Cuprum77/PD2Breadboard/Software/include/bg.h

/* GIMP RGB C-Source image dump (bg.c) */

static const unsigned char background_image[] =
  "\343\030\343\030\343\030\343\030\343\030\343\030\343\030\343\030\343\030\343\030\343"
  "\030\343\030\343\030\343\030\343\030\343\030\343\030\343\030\343\030\343\030\343\030"
  "\343\030\343\030\343\030\343\030\343\030\343\030\343\030\343\030\343\030\343\030\343"
  "\030\343\030\343\030\343\030\343\030\343\030\343\030\343\030\343\030\343\030\343\030"
  "\343\030\343\030\343\030\343\030\343\030\343\030\343\030\343\030\343\030\343\030\343"
  "\030\343\030\343\030\343\030\343\030\343\030\343\030\343\030\343\030\343\030\343\030"
  "\343\030\343\030\343\030\343\030\343\030\343\030\343\030\343\030\343\030\343\030\343"
  "\030\343\030\343\030\343\030\343\030\343\030\343\030\343\030\343\030\343\030\343\030"
  "\343\030\343\030\343\030\343\030\343\030\343\030\343\030\343\030\343\030\343\030\343"
  "\030\343\030\343\030\343\030\343\030\343\030\343\030\343\030\343\030\343\030\343\030"
  "\343\030\343\030\343\030\343\030\343\030\343\030\343\030\343\030\343\030\343\030\343"
  "\030\343\030\343\030\343\030\343\030\343\030\343\030\343\030\343\030\343\030\343\030"
  "\343\030\343\030\343\030\343\030\343\030\343\030\343\030\343\030\343\030\343\030\343"
  "\030\343\030\343\030\343\030\343\030\343\030\343\030\343\030\343\030\343\030\343\030"
  "\343\030\343\030\343\030\343\030\343\030\343\030\343\030\343\030\343\030\343\030\343"
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
  "\377\377\377\377\377\377\377\377\272\326\343\030\343\030\343\030\343\030\343"
  "\030\343\030\343\030\343\030\343\030\343\030\343\030\343\030\343\030\343\030\343\030"
  "\343\030\343\030\343\030\343\030\343\030\343\030\343\030\343\030\343\030\343\030\343"
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
