Cuprum77/PD2Breadboard/Software/include/test.h

#pragma once
const size_t test_size = 37514;
const unsigned char test[] = {
0x00, 0x00, 0x92, 0x86, 0x01, 0x8c, 0x00, 0x80, 0x80, 0x00, 0x01, 0x02, 0x7e, 0x84, 0x00, 0x9e, 0x00, 0x80, 0x80, 0x00, 0x01, 0x13, 0x75, 0x8f, 0x00, 0x01, 0x33, 0x75, 0x89, 0x00, 0x01, 0x20, 0x76, 0x8b, 0x00, 0x9d, 0x00, 0x80, 0x80, 0x00, 0x01, 0x09, 0x7a, 0x8a, 0x00, 0x01, 0x7b, 0x7b, 0x85, 0x00, 0x01, 0xac, 0x7b, 0x85, 0x00, 0x01, 0x15, 0x73, 0x8d, 0x00, 0x05, 0x00, 0x80, 0x80, 0x00, 0x01, 0x07, 0x7b, 0x8c, 0x00, 0x96, 0x00, 0x80, 0x80, 0x00, 0x01, 0x0e, 0x77, 0x8c, 0x00, 0x01, 0x89, 0x7c, 0x87, 0x00, 0x01, 0xff, 0x80, 0x7f, 0x00, 0x01, 0x5d, 0x79, 0x89, 0x00, 0x01, 0x0b, 0x79, 0x8e, 0x00, 0x04, 0x00, 0x80, 0x80, 0x00, 0x01, 0x1b, 0x75, 0x89, 0x00, 0x01, 0x18, 0x76, 0x8b, 0x00, 0x95, 0x00, 0x80, 0x80, 0x00, 0x01, 0x0e, 0x77, 0x8c, 0x00, 0x01, 0xac, 0x7b, 0x85, 0x00, 0x01, 0xf8, 0x7e, 0x84, 0x00, 0x01, 0xda, 0x7c, 0x82, 0x00, 0x01, 0x15, 0x73, 0x8d, 0x00, 0x03, 0x00, 0x80, 0x80, 0x00, 0x01, 0x09, 0x7a, 0x8a, 0x00, 0x02, 0x6f, 0x78, 0x87, 0x00, 0x01, 0x04, 0x7d, 0x88, 0x00, 0x79, 0x00, 0x80, 0x80, 0x00, 0x01, 0x15, 0x73, 0x8d, 0x00, 0x01, 0x26, 0x77, 0x87, 0x00, 0x01, 0x04, 0x7d, 0x88, 0x00, 0x18, 0x00, 0x80, 0x80, 0x00, 0x01, 0x10, 0x76, 0x8a, 0x00, 0x01, 0xd2, 0x7c, 0x81, 0x00, 0x01, 0xf8, 0x7e, 0x84, 0x00, 0x01, 0xff, 0x80, 0x7f, 0x00, 0x01, 0x3b, 0x75, 0x8a, 0x00, 0x03, 0x00, 0x80, 0x80, 0x00, 0x01, 0x1d, 0x73, 0x8d, 0x00, 0x01, 0xea, 0x7d, 0x82, 0x00, 0x01, 0xee, 0x80, 0x80, 0x00, 0x01, 0x39, 0x76, 0x8b, 0x00, 0x79, 0x00, 0x80, 0x80, 0x00, 0x01, 0x1b, 0x79, 0x82, 0x00, 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
